42Maxim/Vibe-Hardware-Claude-Fable-5.1-Build-Day/build/ref/contact.png

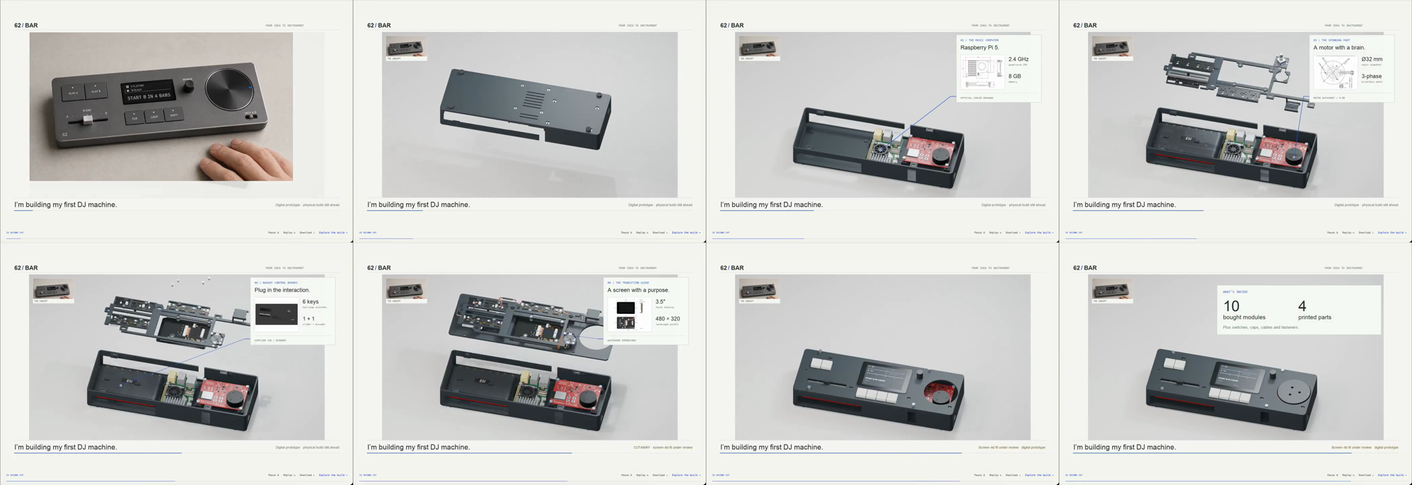
build/ref/contact.png
