42Maxim/Vibe-Hardware-Claude-Fable-5.1-Build-Day/build/ref/f01.png

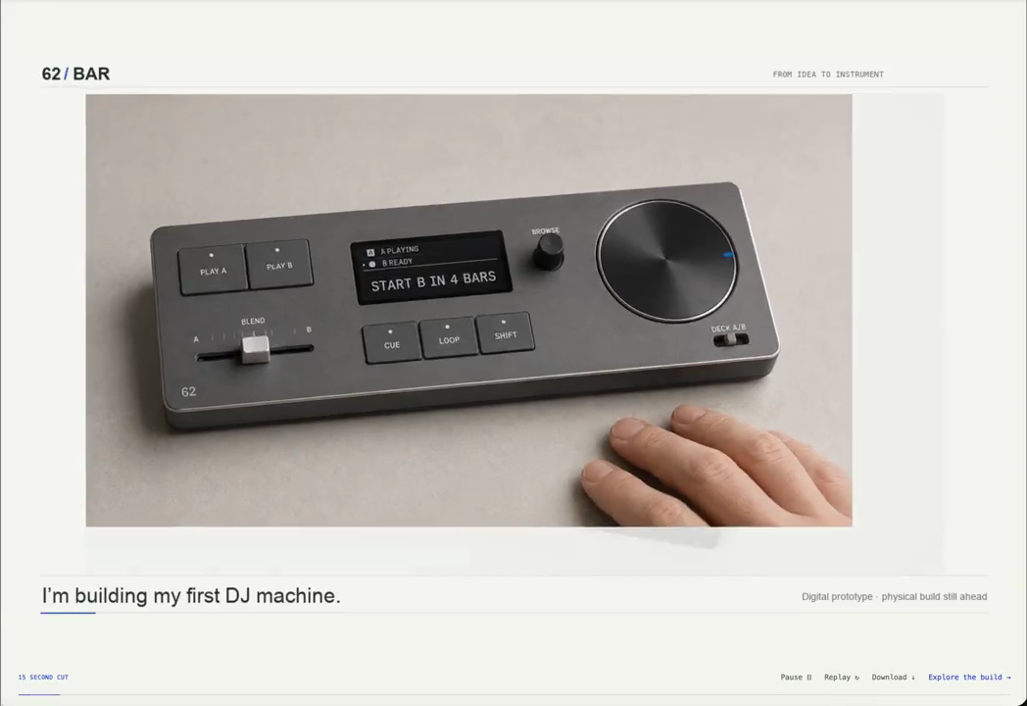
build/ref/f01.png
